Gtrx0/cpm43/CPM title/CPM3.2.png

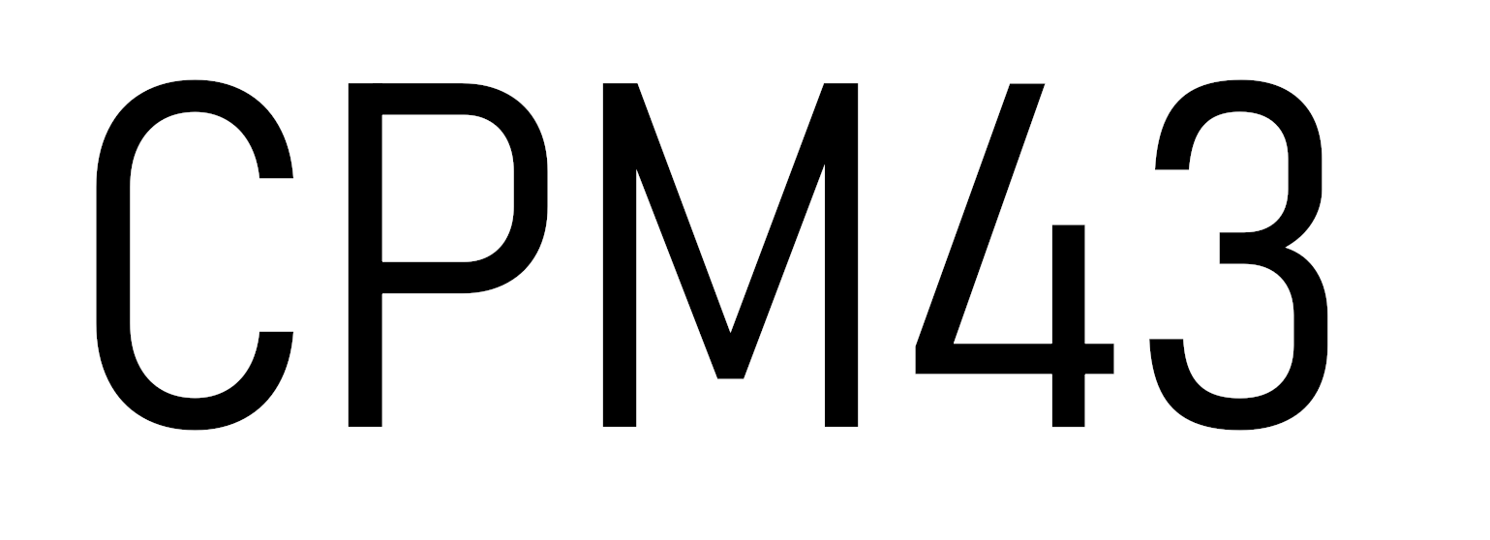
CPM title/CPM3.2.png
